Hackin7/cg2111a_we_ball/arduino/Alex/1_comms_format.ino

/*
 * 
 * Alex Communication Routines.
 * 
 */

void dbprintf(char *format, ...) {
  va_list args;
  char buffer[128];
  va_start(args, format);
  vsprintf(buffer, format, args);
  sendMessage(buffer);
} 

/* --------------------------------------------------------------------------------*/
void sendStatus()
{
  // Implement code to send back a packet containing key
  // information like leftTicks, rightTicks, leftRevs, rightRevs
  // forwardDist and reverseDist
  // Use the params array to store this information, and set the
  // packetType and command files accordingly, then use sendResponse
  // to send out the packet. See sendMessage on how to use sendResponse.
  //

  TPacket statusPacket;
  statusPacket.packetType = PACKET_TYPE_RESPONSE;
  statusPacket.command = RESP_STATUS;
  statusPacket.params[0] = leftForwardTicks;
  statusPacket.params[1] = rightForwardTicks;
  statusPacket.params[2] = leftReverseTicks;
  statusPacket.params[3] = rightReverseTicks;
  statusPacket.params[4] = leftForwardTicksTurns;
  statusPacket.params[5] = rightForwardTicksTurns;
  statusPacket.params[6] = leftReverseTicksTurns;
  statusPacket.params[7] = rightReverseTicksTurns;
  statusPacket.params[8] = forwardDist;
  statusPacket.params[9] = reverseDist;
  sendResponse(&statusPacket);

}

void sendMessage(const char *message)
{
  // Sends text messages back to the Pi. Useful
  // for debugging.
  
  TPacket messagePacket;
  messagePacket.packetType=PACKET_TYPE_MESSAGE;
  strncpy(messagePacket.data, message, MAX_STR_LEN);
  sendResponse(&messagePacket);
}

void sendBadPacket()
{
  // Tell the Pi that it sent us a packet with a bad
  // magic number.
  
  TPacket badPacket;
  badPacket.packetType = PACKET_TYPE_ERROR;
  badPacket.command = RESP_BAD_PACKET;
  sendResponse(&badPacket);
  
}

void sendBadChecksum()
{
  // Tell the Pi that it sent us a packet with a bad
  // checksum.
  
  TPacket badChecksum;
  badChecksum.packetType = PACKET_TYPE_ERROR;
  badChecksum.command = RESP_BAD_CHECKSUM;
  sendResponse(&badChecksum);  
}

void sendBadCommand()
{
  // Tell the Pi that we don't understand its
  // command sent to us.
  
  TPacket badCommand;
  badCommand.packetType=PACKET_TYPE_ERROR;
  badCommand.command=RESP_BAD_COMMAND;
  sendResponse(&badCommand);
}

void sendBadResponse()
{
  TPacket badResponse;
  badResponse.packetType = PACKET_TYPE_ERROR;
  badResponse.command = RESP_BAD_RESPONSE;
  sendResponse(&badResponse);
}

void sendOK()
{
  TPacket okPacket;
  okPacket.packetType = PACKET_TYPE_RESPONSE;
  okPacket.command = RESP_OK;
  sendResponse(&okPacket);  
}

void sendResponse(TPacket *packet)
{
  // Takes a packet, serializes it then sends it out
  // over the serial port.
  char buffer[PACKET_SIZE];
  int len;

  len = serialize(buffer, packet, sizeof(TPacket));
  writeSerial(buffer, len);
}

/* --------------------------------------------------------------------------------*/
void handleCommand(TPacket *command)
{
  switch(command->command)
  {
    // For movement commands, param[0] = distance, param[1] = speed.
    case COMMAND_FORWARD:
        forward((float) command->params[0], (float) command->params[1]);
        sendOK();
      break;
    case COMMAND_REVERSE:
        backward((float) command->params[0], (float) command->params[1]);
        sendOK();
      break;
    case COMMAND_TURN_LEFT:
        left((float) command->params[0], (float) command->params[1]);
        sendOK();
      break;
    case COMMAND_TURN_RIGHT:
	    right((float) command->params[0], (float) command->params[1]);
        sendOK();
      break;
    case COMMAND_STOP:
        stop();
        sendOK();
      break;
    case COMMAND_GET_STATS:
        sendStatus();
        sendOK();
      break;
    case COMMAND_CLEAR_STATS:
        clearOneCounter(command->params[0]);
        sendOK();
      break;
    
    /*
     * Implement code for other commands here.
     * 
     */
        
    default:
      sendBadCommand();
  }
}

void waitForHello()
{
  int exit=0;

  while(!exit)
  {
    TPacket hello;
    TResult result;
    
    do
    {
      result = readPacket(&hello);
    } while (result == PACKET_INCOMPLETE);

    if(result == PACKET_OK)
    {
      if(hello.packetType == PACKET_TYPE_HELLO)
      {
     

        sendOK();
        exit=1;
      }
      else
        sendBadResponse();
    }
    else
      if(result == PACKET_BAD)
      {
        sendBadPacket();
      }
      else
        if(result == PACKET_CHECKSUM_BAD)
          sendBadChecksum();
  } // !exit
}



void handlePacket(TPacket *packet)
{
  switch(packet->packetType)
  {
    case PACKET_TYPE_COMMAND:
      handleCommand(packet);
      break;

    case PACKET_TYPE_RESPONSE:
      break;

    case PACKET_TYPE_ERROR:
      break;

    case PACKET_TYPE_MESSAGE:
      break;

    case PACKET_TYPE_HELLO:
      break;
  }
}
